logical/telepathy/amplifier-board/amp-board.sch

## KiCad design amplifier-board/amp-board.sch (2018-01-20, an earlier design)

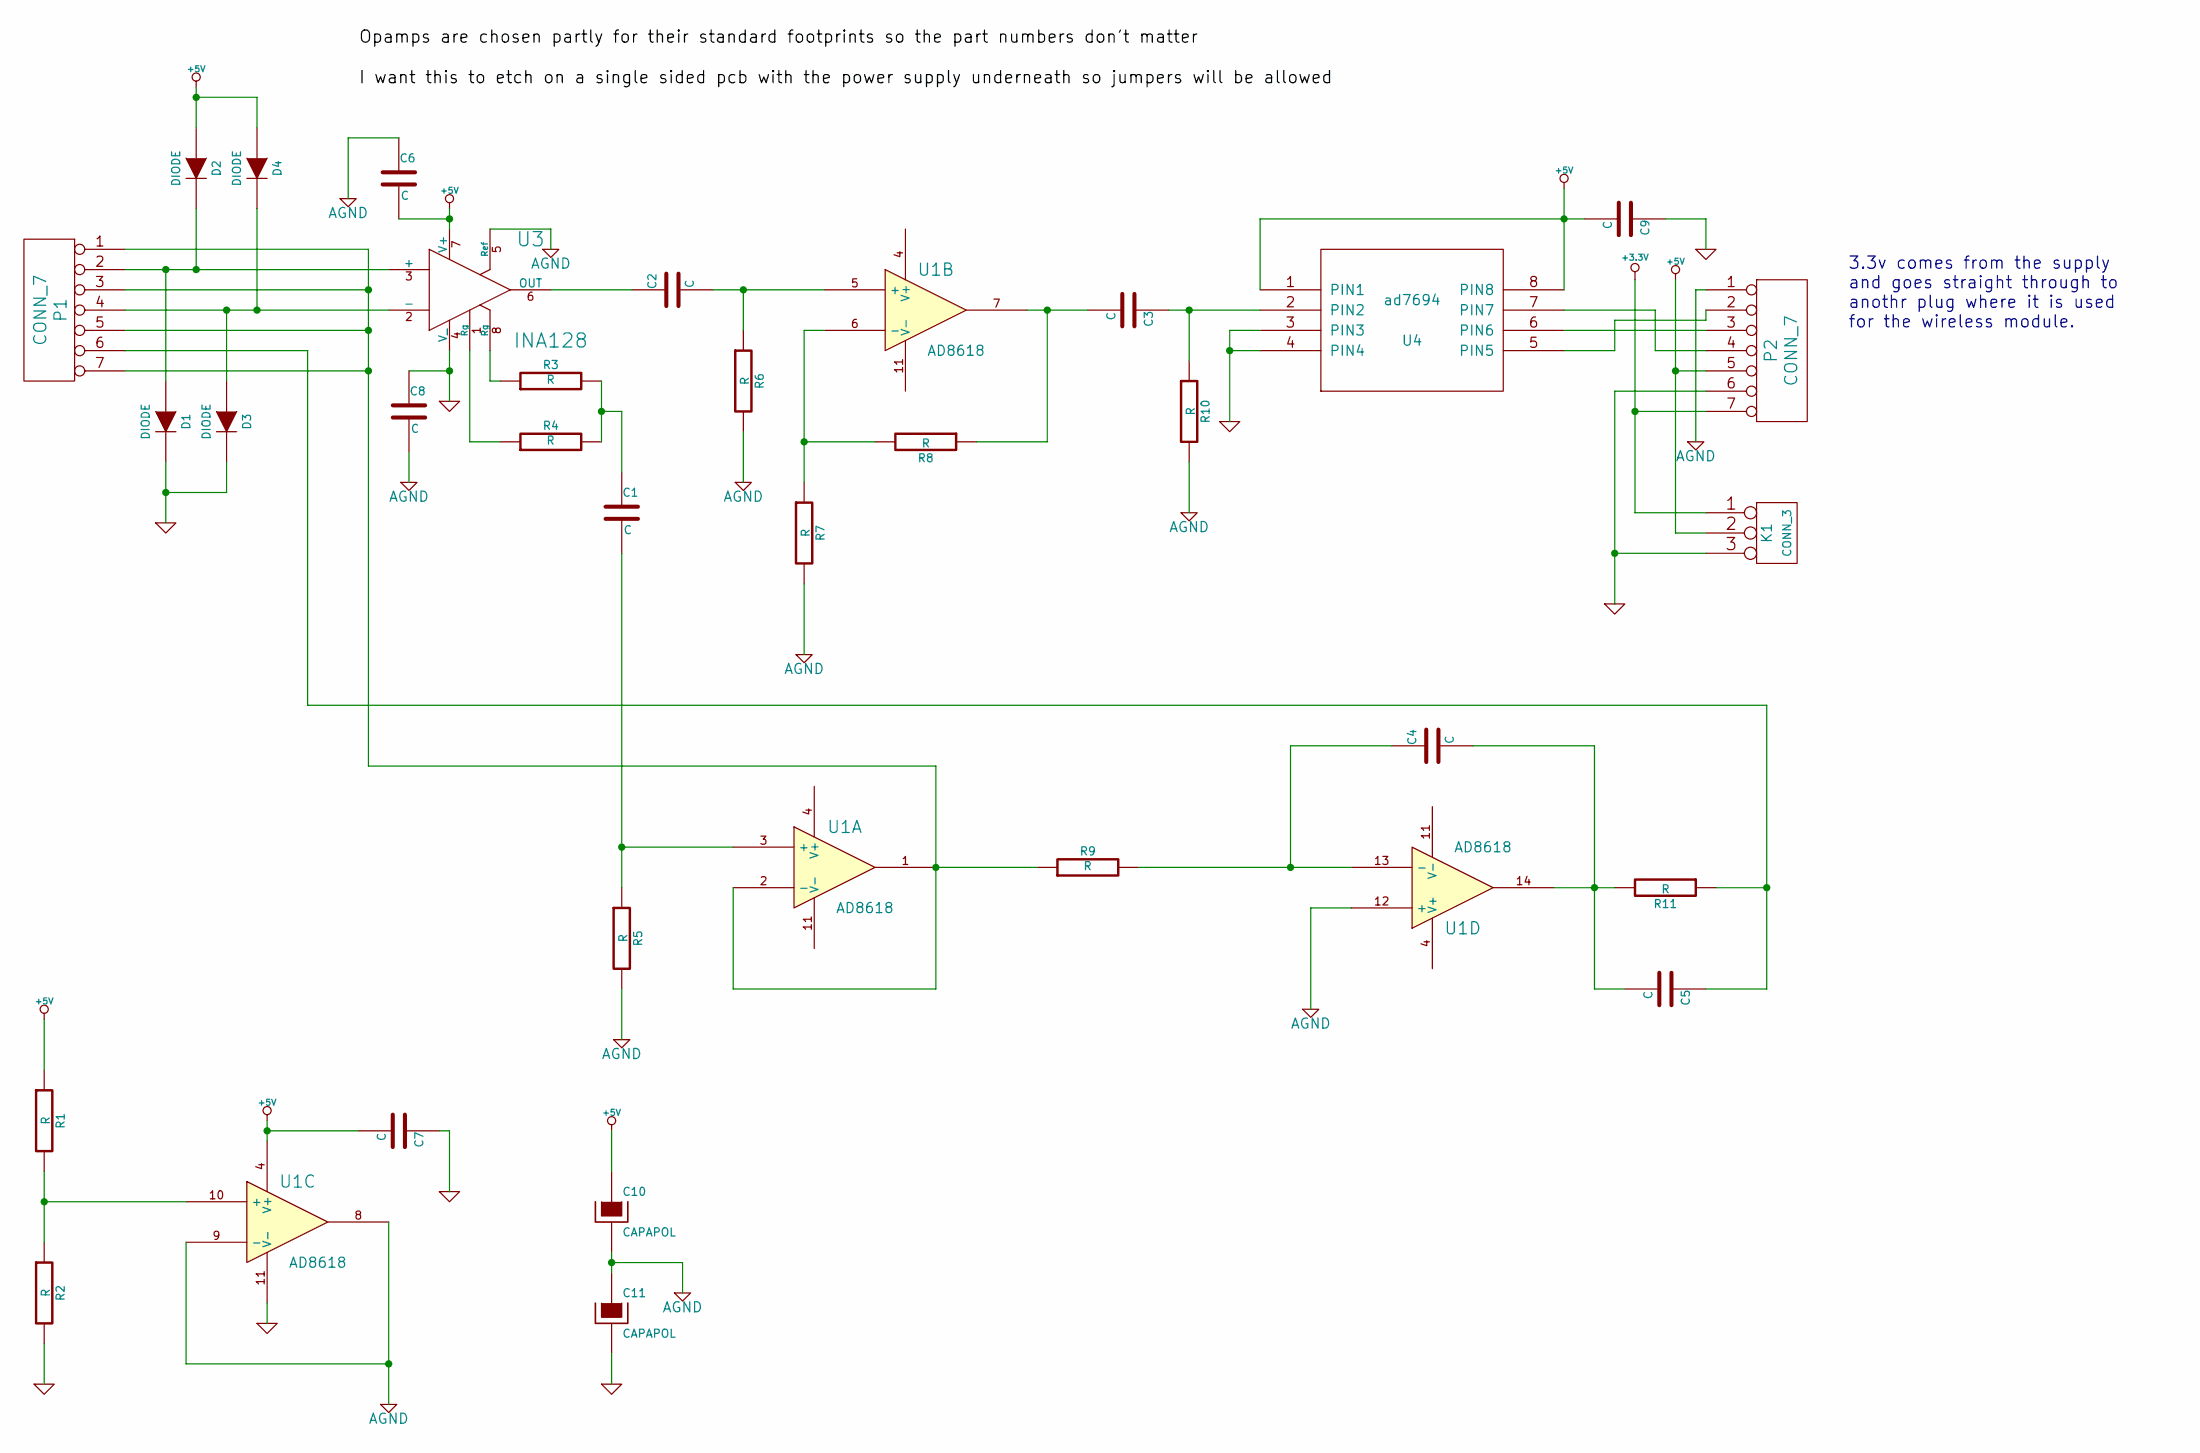
[picture p12: schematic amp-board.sch]

Parts:
C1, C2, C3, C4, C5, C6, C7, C8, C9: C
C10, C11: CAPAPOL
D1, D2, D3, D4: DIODE
K1: CONN_3
P1, P2: CONN_7
R1, R2, R3, R4, R5, R6, R7, R8, R9, R10, R11: R
U1: AD8618
U3: INA128
U4: ad7694; MODULE

Connections:
+3.3V: K1.1, P2.7
+5V: C6.2, C7.2, C9.2, C10.1, D2.1 (A), D4.1 (A), K1.2 (PM), P2.5, R1.1, U1.4 (V+), U3.7 (V+), U4.1 (PIN1), U4.8 (PIN8)
AGND: C6.1, C8.2, C10.2, C11.1, P2.1, R5.2, R6.2, R7.2, R10.2, U1.8, U1.9 (-), U1.12 (+), U3.5 (Ref)
GND: C7.1, C8.1, C9.1, C11.2, D1.2 (K), D3.2 (K), K1.3, P2.6, R2.2, U1.11 (V-), U3.4 (V_), U4.3 (PIN3), U4.4 (PIN4)
unnamed: C1.1, R3.2, R4.2
unnamed: C1.2, R5.1, U1.3 (+)
unnamed: C2.1, U3.6 (OUT)
unnamed: C2.2, R6.1, U1.5 (+)
unnamed: C3.1, R10.1, U4.2 (PIN2)
unnamed: C3.2, R8.1, U1.7
unnamed: C4.1, R9.2, U1.13 (-)
unnamed: C4.2, C5.2, R11.2, U1.14
unnamed: C5.1, P1.6, R11.1
unnamed: D1.1 (A), D2.2 (K), P1.2, U3.3 (+)
unnamed: D3.1 (A), D4.2 (K), P1.4, U3.2 (-)
unnamed: P1.1, P1.3, P1.5, P1.7, R9.1, U1.1, U1.2 (-)
unnamed: P2.2, U4.5 (PIN5)
unnamed: P2.3, U4.6 (PIN6)
unnamed: P2.4, U4.7 (PIN7)
unnamed: R1.2, R2.1, U1.10 (+)
unnamed: R3.1, U3.8 (Rg)
unnamed: R4.1, U3.1 (Rg)
unnamed: R7.1, R8.2, U1.6 (-)

Notes on the sheet:
3.3v comes from the supply and goes straight through to anothr plug where it is used for the wireless module.
