logical/telepathy/telepathy-kicad/telepathy.sch

## KiCad design telepathy-kicad/telepathy.sch (2018-01-20, an earlier design)

Schematic: telepathy.sch

Parts:
C1, C2, C3, C6, C18: CP
C4, C5, C7, C8, C9, C10, C11, C12, C13, C14, C15, C16, C17, C19: C
D1, D2, D3, D4, D8: DIODE
D5, D7: LED
K1: CONN_3
P1: CONN_2
P2, P3, P4, P5: CONN_4
P6, P7, P8: CONN_1
Q1, Q2, Q3, Q4, Q5, Q6, Q7, Q8: NPN
R1, R2, R3, R4, R5, R6, R7, R8, R9, R10, R11, R12, R13, R14, R15, R16, R17, R18, R19, R20, R21, R22: R
U1: AMS1117
U2: ad8630
U4: ADG409; MODULE
U5, U8: DIL8; MODULE
U6: MCP4131
U7: DIL28; MODULE
U9: MODULE34; MODULE
U10: 7833

Notes on the sheet:
these pins are swapped because the routing was difficult pin 23 controls channel 3 pin 24 controls channel 4 pin 25 controls channel 1 pin 26 controls channel 2
